jd3096-mpy/MPY-CASSETTE-PLAYER/EVA-2.jpg

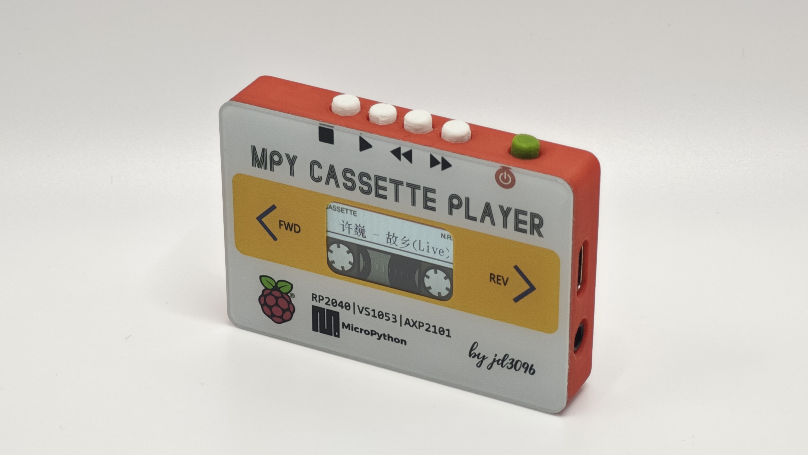
EVA-2.jpg
