jd3096-mpy/MPY-CASSETTE-PLAYER/src/img/poweroff.jpg

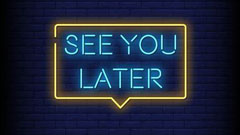
src/img/poweroff.jpg
