jd3096-mpy/MPY-CASSETTE-PLAYER/src/img/update.jpg

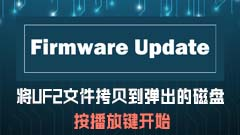
src/img/update.jpg
